DQUEROL/Respirador-DQ3D-NICA/03 Accesorios, valvulas, sensores/peep/PANDApeep+Gen2+PEEP+valve/images/base_gen2.png

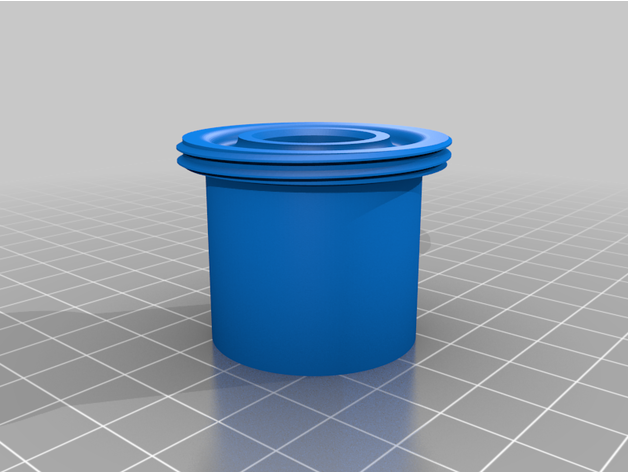
03 Accesorios, valvulas, sensores/peep/PANDApeep+Gen2+PEEP+valve/images/base_gen2.png
