DQUEROL/Respirador-DQ3D-NICA/03 Accesorios, valvulas, sensores/peep/PANDApeep+Gen2+PEEP+valve/images/flatspring_gen2_inline.png

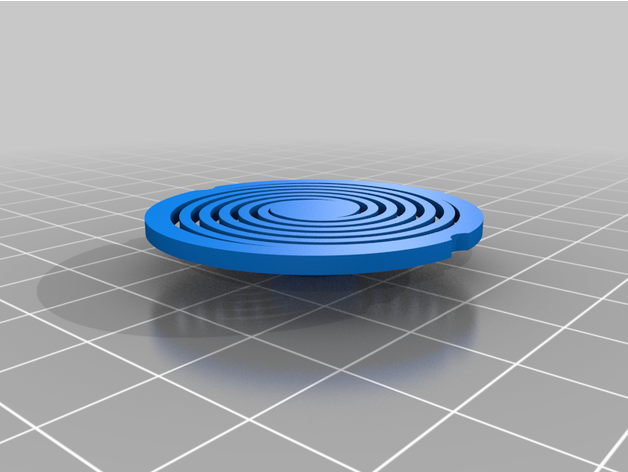
03 Accesorios, valvulas, sensores/peep/PANDApeep+Gen2+PEEP+valve/images/flatspring_gen2_inline.png
