DQUEROL/Respirador-DQ3D-NICA/03 Accesorios, valvulas, sensores/sensores/bmp280/BME280-I2C-Humidity-Pressure-Temperature-Sensor-Module-Connections.png

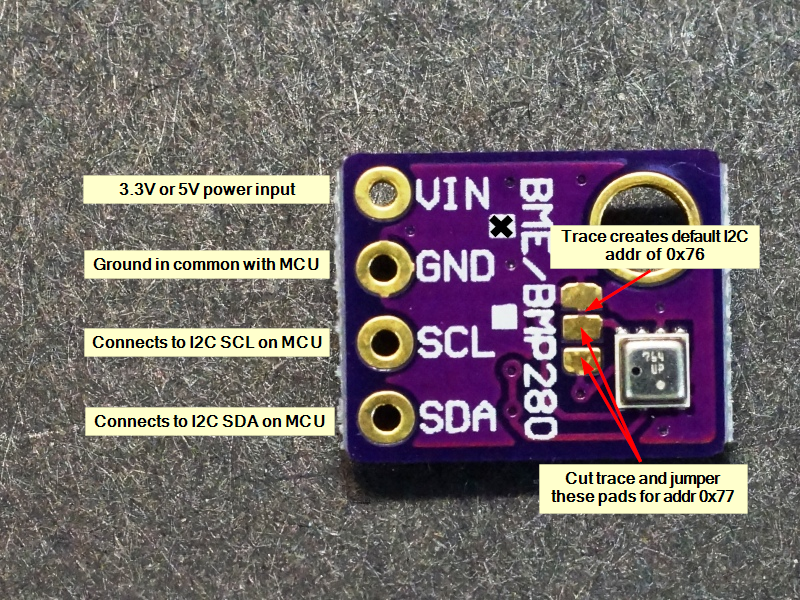
03 Accesorios, valvulas, sensores/sensores/bmp280/BME280-I2C-Humidity-Pressure-Temperature-Sensor-Module-Connections.png
