DQUEROL/Respirador-DQ3D-NICA/03 Accesorios, valvulas, sensores/sensores/bmp280/BMP280.jpg

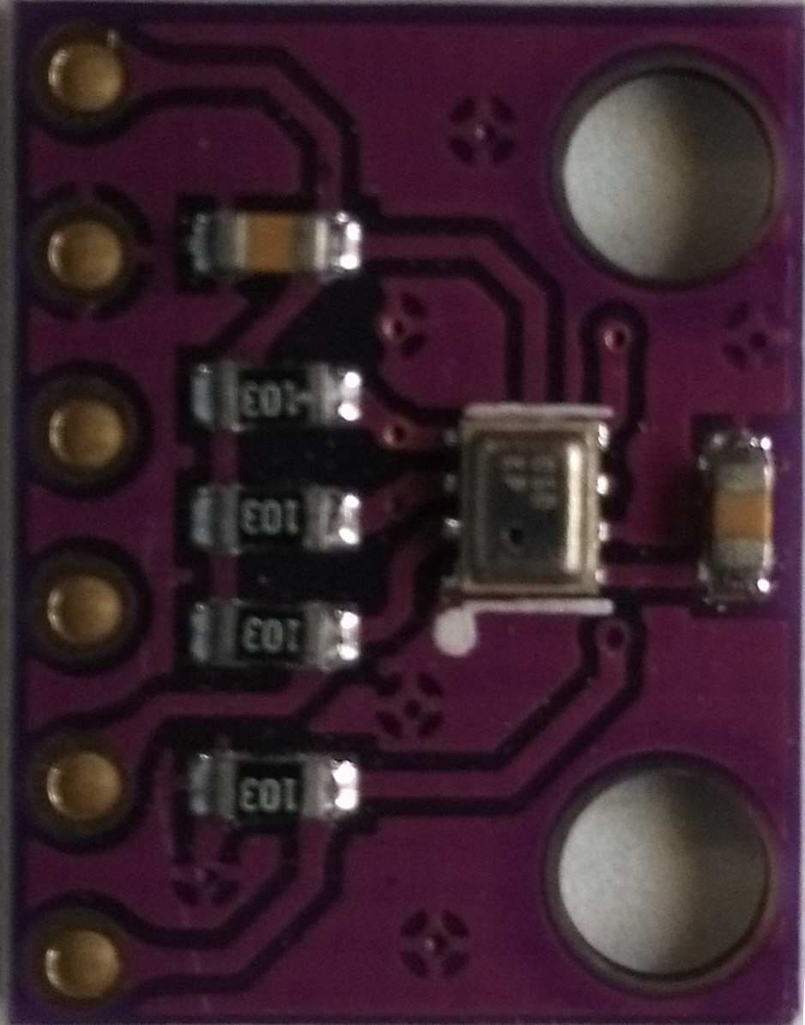
03 Accesorios, valvulas, sensores/sensores/bmp280/BMP280.jpg
