DQUEROL/Respirador-DQ3D-NICA/03 Accesorios, valvulas, sensores/sensores/bmp280/curvas presion.jpg

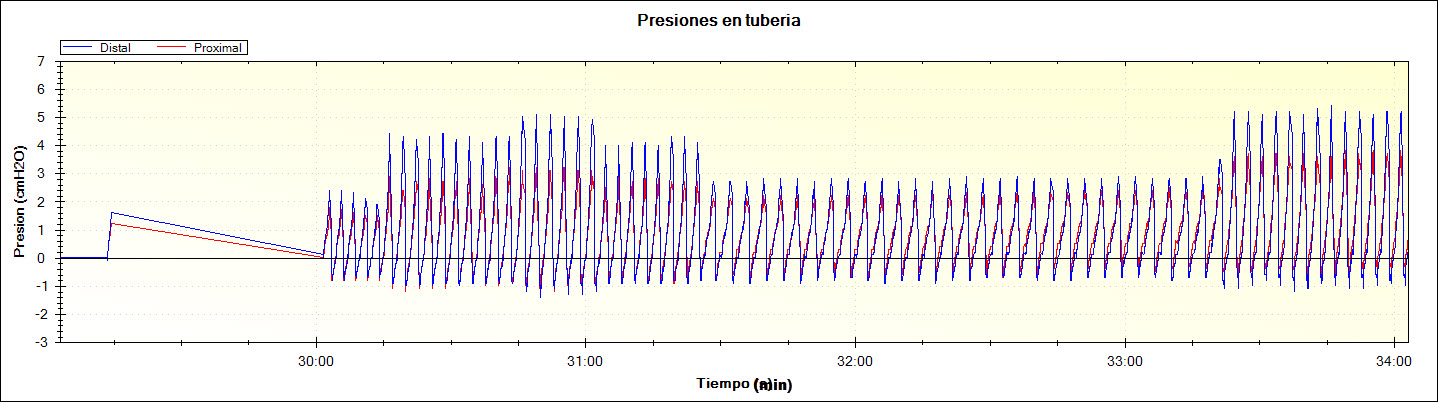
03 Accesorios, valvulas, sensores/sensores/bmp280/curvas presion.jpg
