DQUEROL/Respirador-DQ3D-NICA/03 Accesorios, valvulas, sensores/sensores/bmp280/no usado/45538157714_bf0bbf35da_b.jpg

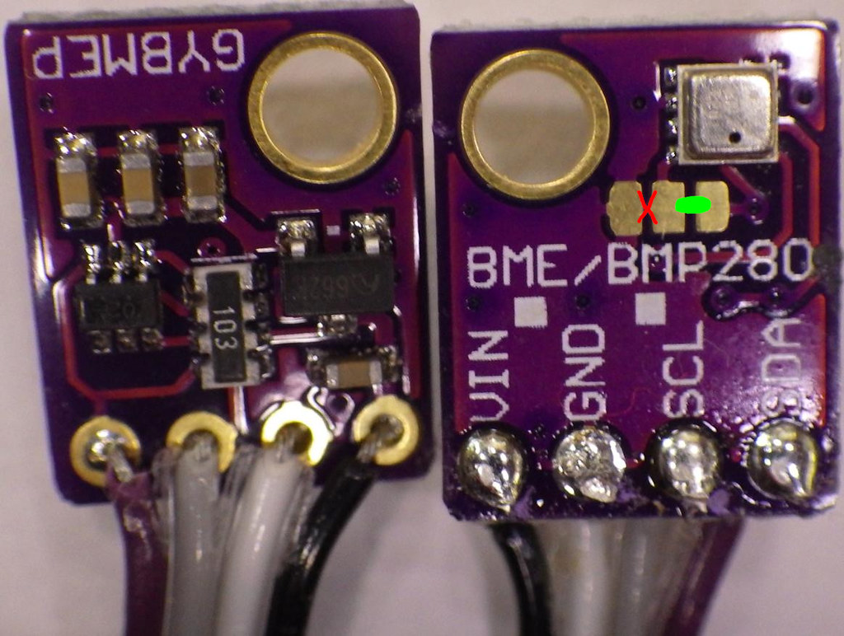
03 Accesorios, valvulas, sensores/sensores/bmp280/no usado/45538157714_bf0bbf35da_b.jpg
