DQUEROL/Respirador-DQ3D-NICA/03 Accesorios, valvulas, sensores/sensores/BMP 388/2020-03-17T10 33 51.334Z-pspv280.jpg

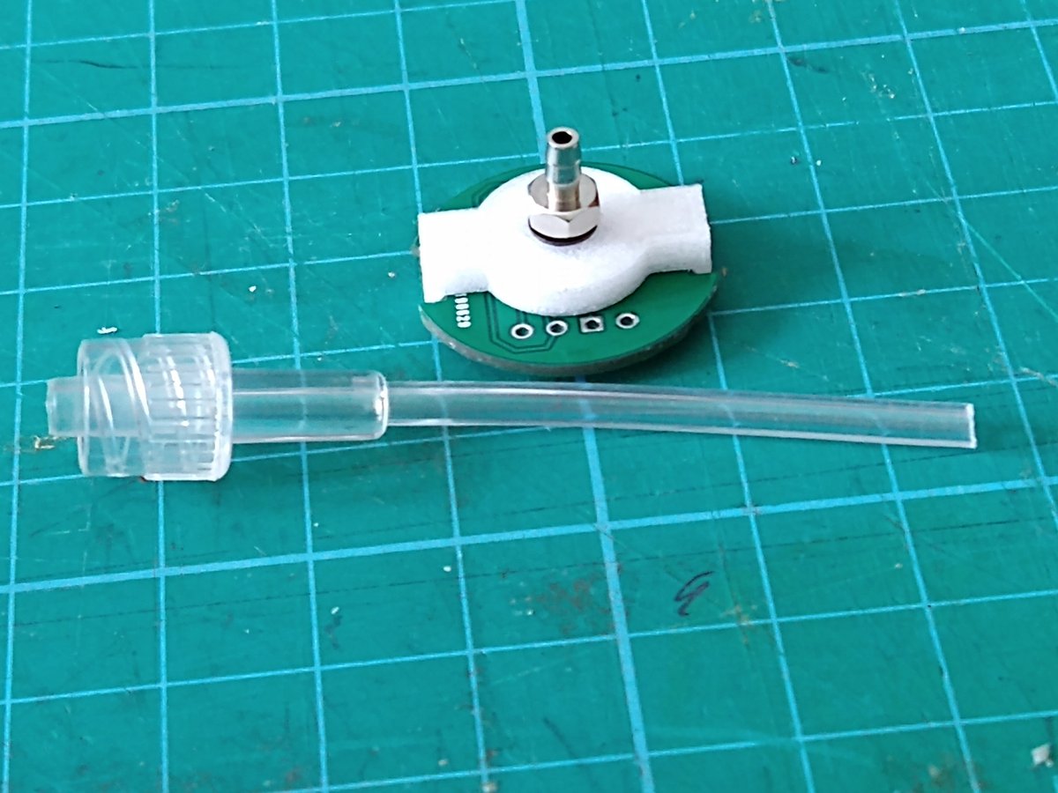
03 Accesorios, valvulas, sensores/sensores/BMP 388/2020-03-17T10 33 51.334Z-pspv280.jpg
