DQUEROL/Respirador-DQ3D-NICA/05 Fotos y videos/IMG_20200427_112459.jpg

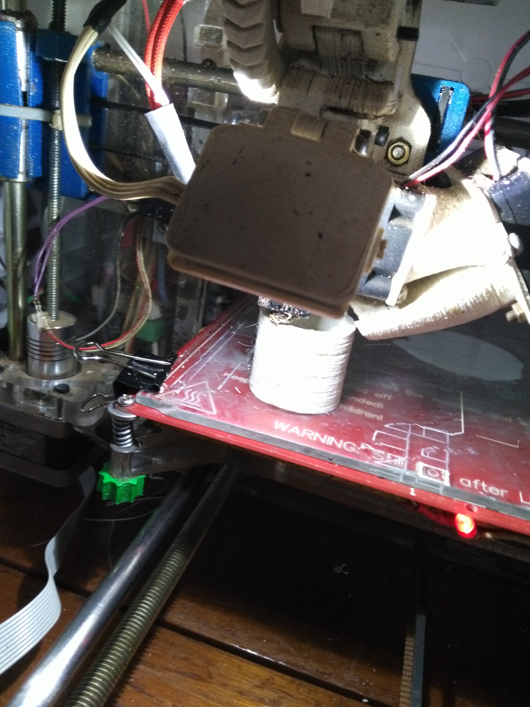
05 Fotos y videos/IMG_20200427_112459.jpg
