DQUEROL/Respirador-DQ3D-NICA/05 Fotos y videos/IMG_20200502_051914.jpg

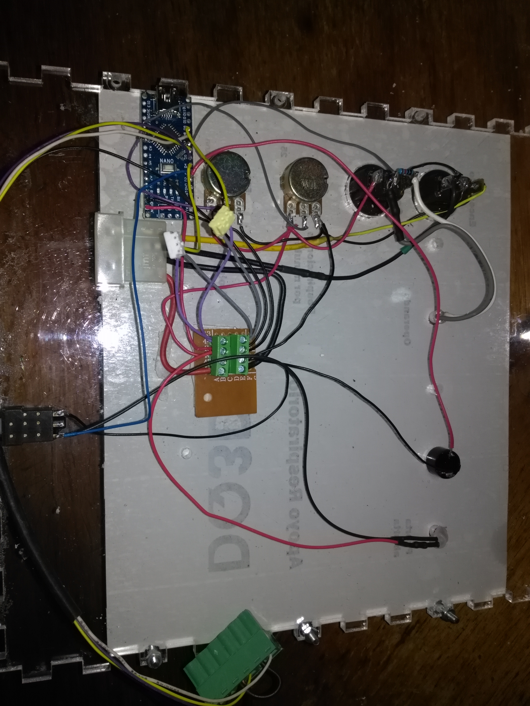
05 Fotos y videos/IMG_20200502_051914.jpg
