DQUEROL/Respirador-DQ3D-NICA/05 Fotos y videos/IMG_20200504_171438.jpg

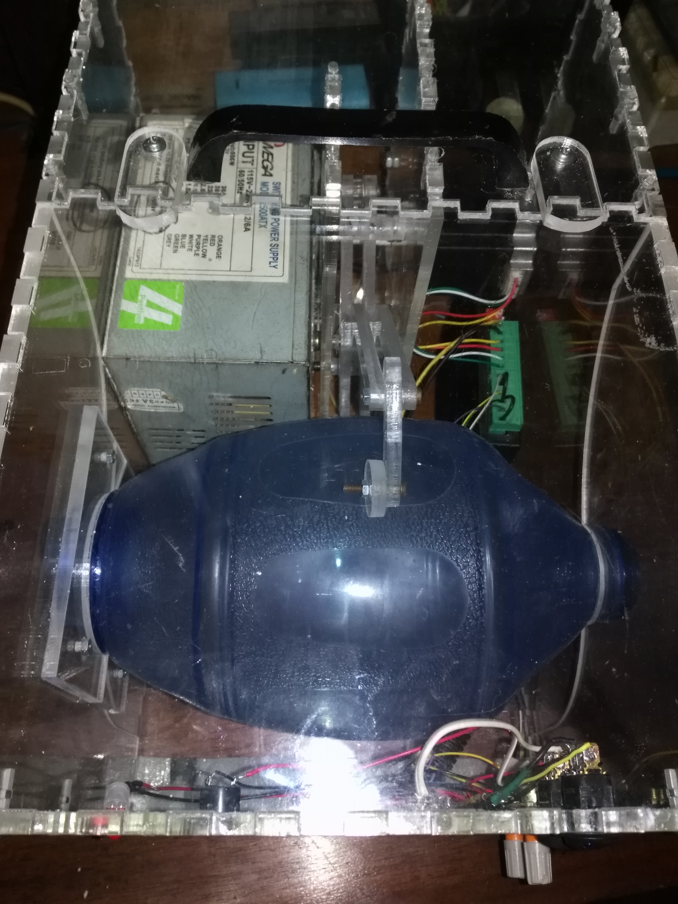
05 Fotos y videos/IMG_20200504_171438.jpg
