DQUEROL/Respirador-DQ3D-NICA/05 Fotos y videos/IMG_20200519_070126.jpg

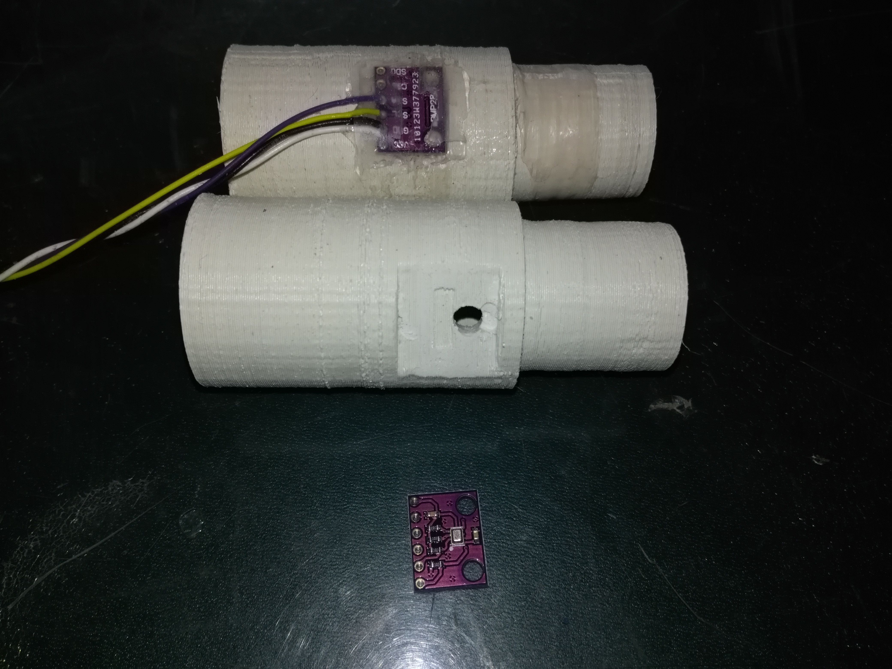
05 Fotos y videos/IMG_20200519_070126.jpg
