DQUEROL/Respirador-DQ3D-NICA/05 Fotos y videos/stopper-knot.jpg

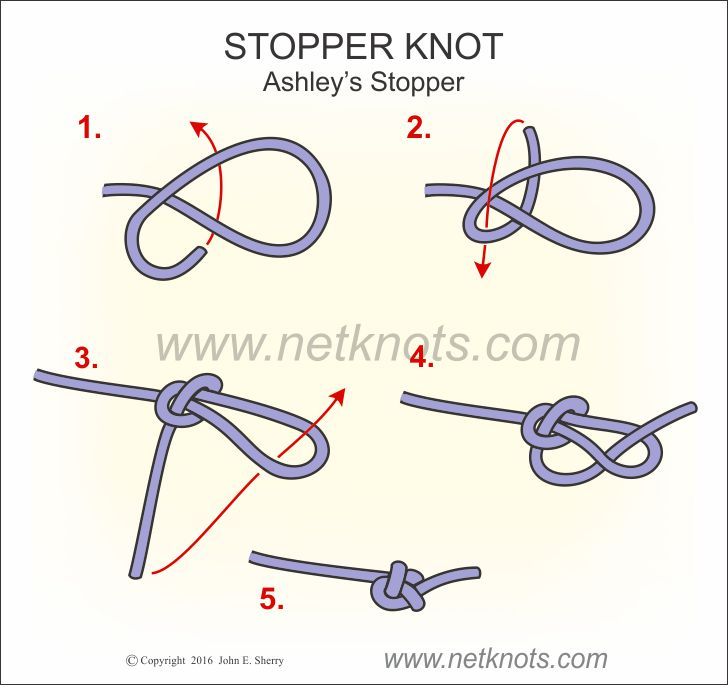
05 Fotos y videos/stopper-knot.jpg
